Labbaker/SeniorDesign/BeaconBoard/Adafruit-FRAM-Breakout-PCB-master/Adafruit I2C FRAM.brd

## EAGLE design BeaconBoard/Adafruit-FRAM-Breakout-PCB-master/Adafruit I2C FRAM.brd (2018-10-22)

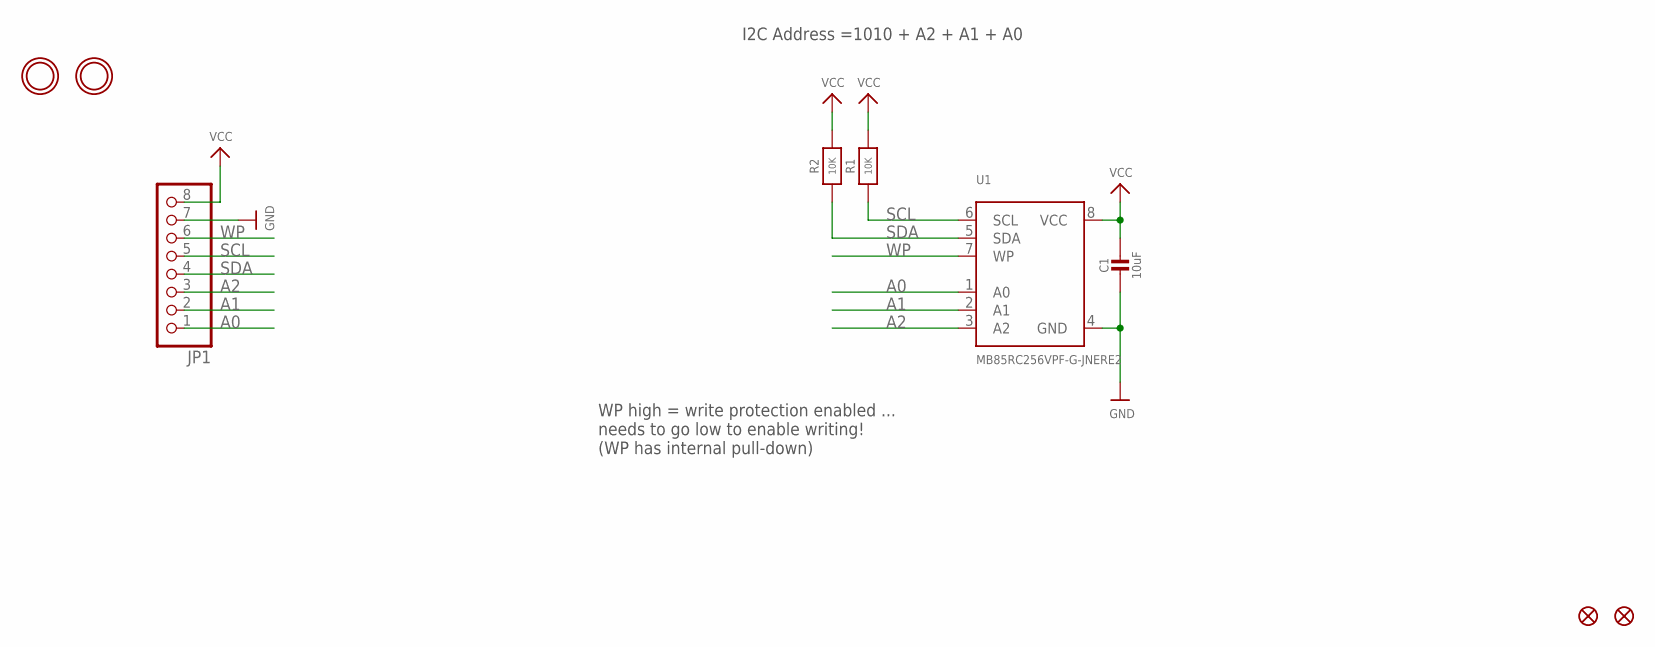
[picture p47: schematic Adafruit I2C FRAM.sch]

Parts:
C1: 10uF; _0805MP
FID1, FID2: FIDUCIAL""; FIDUCIAL_1MM
JP1: HEADER-1X870MIL; 1X08_ROUND_70
R1, R2: 10K; _0805MP
U1: MB85RC256VPF-G-JNERE2; SOIC8_208MIL
U$5, U$6: MOUNTINGHOLE2.5; MOUNTINGHOLE_2.5_PLATED

Connections:
A0: JP1.1, U1.1 (A0)
A1: JP1.2, U1.2 (A1)
A2: JP1.3, U1.3 (A2)
GND: C1.2, JP1.7, U1.4 (GND)
SCL: JP1.5, R1.1, U1.6 (SCL)
SDA: JP1.4, R2.1, U1.5 (SDA)
VCC: C1.1, JP1.8, R1.2, R2.2, U1.8 (VCC)
WP: JP1.6, U1.7 (WP)

Notes on the sheet:
WP high = write protection enabled ... needs to go low to enable writing! (WP has internal pull-down)
I2C Address =1010 + A2 + A1 + A0

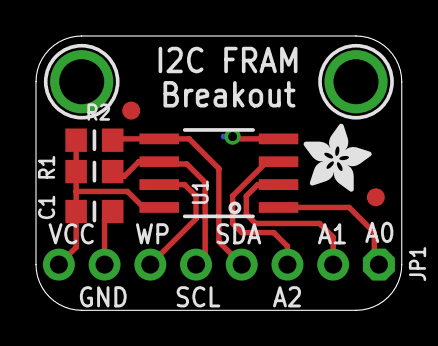
[picture p48: board Adafruit I2C FRAM.brd from above]

Board: 2 copper layers, 20.3 x 15.2 mm, 10 parts (0 on the bottom side), 8 nets.

Other parts of the board:
U$4: ADAFRUIT_3.5MM
